carrotIndustries/blinkenbike/hw/pool/3d_models/cache/6d752bc3-29b3-45df-8cf2-1e3aacefbcc6/3d_models/passive/capacitor/C_0805_2012Metric.step

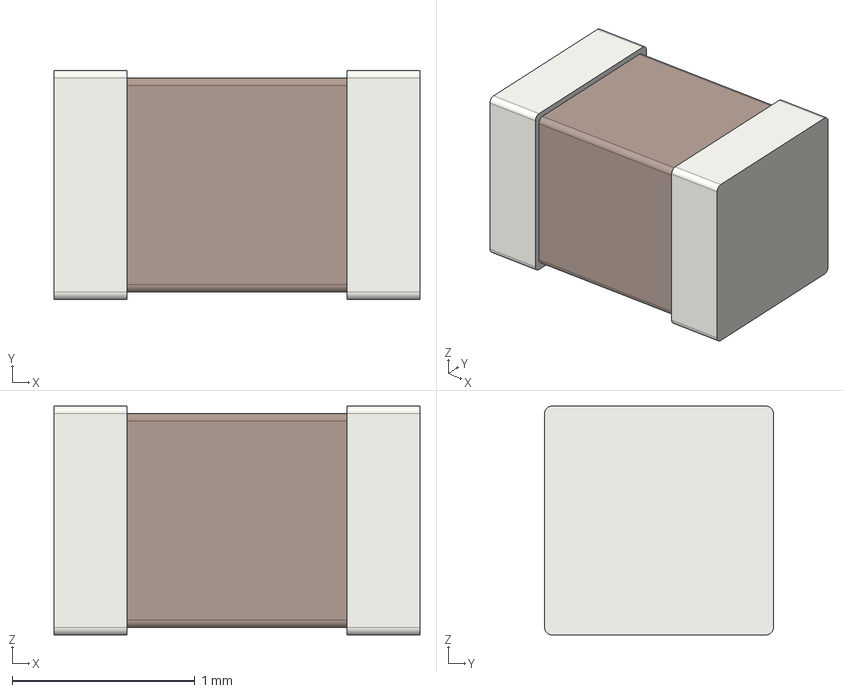
[picture p20: CAD file, 2023-03-11]
hw/pool/3d_models/cache/6d752bc3-29b3-45df-8cf2-1e3aacefbcc6/3d_models/passive/capacitor/C_0805_2012Metric.step
2.00 x 1.25 x 1.25 mm
